Windfisch/midikraken/firmware/src/str_writer.rs

use core::cmp::min;
use core::fmt;

// stolen from https://stackoverflow.com/a/50201632

pub struct WriteTo<'a> {
	buffer: &'a mut [u8],
	// on write error (i.e. not enough space in buffer) this grows beyond
	// `buffer.len()`.
	used: usize,
}

impl<'a> WriteTo<'a> {
	pub fn new(buffer: &'a mut [u8]) -> Self {
		WriteTo { buffer, used: 0 }
	}

	pub fn as_str(self) -> Option<&'a str> {
		if self.used <= self.buffer.len() {
			// only successful concats of str - must be a valid str.
			use core::str::from_utf8_unchecked;
			Some(unsafe { from_utf8_unchecked(&self.buffer[..self.used]) })
		}
		else {
			None
		}
	}
}

impl<'a> fmt::Write for WriteTo<'a> {
	fn write_str(&mut self, s: &str) -> fmt::Result {
		if self.used > self.buffer.len() {
			return Err(fmt::Error);
		}
		let remaining_buf = &mut self.buffer[self.used..];
		let raw_s = s.as_bytes();
		let write_num = min(raw_s.len(), remaining_buf.len());
		remaining_buf[..write_num].copy_from_slice(&raw_s[..write_num]);
		self.used += raw_s.len();
		if write_num < raw_s.len() {
			Err(fmt::Error)
		}
		else {
			Ok(())
		}
	}
}

#[allow(unused_macros)]
macro_rules! slfmt_fallible {
		($dst:expr, $($arg:tt)*) => {{
			let mut w = WriteTo::new($dst);
			match write!(w, $($arg)*) {
				Ok(_) => Ok(w.as_str().unwrap()),
				Err(e) => Err(e)
			}
		}}
}
#[allow(unused_macros)]
macro_rules! slfmtln_fallible {
		($dst:expr, $($arg:tt)*) => {{
			let mut w = WriteTo::new($dst);
			match writeln!(w, $($arg)*) {
				Ok(_) => Ok(w.as_str().unwrap()),
				Err(e) => Err(e)
			}
		}}
}
#[allow(unused_macros)]
macro_rules! slfmtln {
		($dst:expr, $($arg:tt)*) => {{ slfmtln_fallible!($dst, $($arg)*).unwrap() }}
}

#[allow(unused_macros)]
macro_rules! slfmt {
		($dst:expr, $($arg:tt)*) => {{ slfmt_fallible!($dst, $($arg)*).unwrap() }}
}
